connorwhite-online/pneuma/firmware/session/src/state.rs

//! The interaction state machine: Sleep → Connect → Capture → Converse → Forget.
//! Provider- and hardware-agnostic — it drives `dyn Provider` over `dyn` HAL
//! traits, so the same logic runs on mocks (laptop) or real drivers (device).
//! See docs/ARCHITECTURE.md §2.

use std::error::Error;
use std::path::PathBuf;

use crate::config::DeviceConfig;
use crate::hal::{AudioIn, AudioOut, Camera, Modem, WakeReason};
use crate::memory::Memory;
use crate::provider::{MemoryOp, Provider, SessionEvent, SessionOpts};
use crate::tool::ToolRegistry;

const SYSTEM_PROMPT: &str = "You are Pneuma, a concise, warm voice companion. \
Answer briefly. Use the user's memory for context. Only mention what you see when asked.";

#[derive(Debug, Clone, Copy, PartialEq, Eq)]
pub enum State {
    Sleep,
    Connect,
    Capture,
    Converse,
    Forget,
}

pub struct Pneuma {
    mic: Box<dyn AudioIn>,
    speaker: Box<dyn AudioOut>,
    camera: Box<dyn Camera>,
    modem: Box<dyn Modem>,
    provider: Box<dyn Provider>,
    memory: Memory,
    memory_path: PathBuf,
    config: DeviceConfig,
    tools: ToolRegistry,
}

impl Pneuma {
    #[allow(clippy::too_many_arguments)]
    pub fn new(
        mic: Box<dyn AudioIn>,
        speaker: Box<dyn AudioOut>,
        camera: Box<dyn Camera>,
        modem: Box<dyn Modem>,
        provider: Box<dyn Provider>,
        memory: Memory,
        memory_path: PathBuf,
        config: DeviceConfig,
    ) -> Self {
        Pneuma {
            mic,
            speaker,
            camera,
            modem,
            provider,
            memory,
            memory_path,
            config,
            tools: crate::tool::default_registry(),
        }
    }

    pub fn memory(&self) -> &Memory {
        &self.memory
    }

    /// Run one full interaction, triggered by a wake event from the wake island.
    pub fn run_once(&mut self, wake: WakeReason) -> Result<(), Box<dyn Error>> {
        // CONNECT — bring the cellular link up and open a provider session.
        println!("  [state] {:?}", State::Connect);
        if !self.modem.is_online() {
            self.modem.connect();
        }
        let opts = SessionOpts {
            model: self.config.model.clone(),
            memory_context: self.memory.to_context(),
            system_prompt: SYSTEM_PROMPT.to_string(),
        };
        println!(
            "  [provider:{}] starting session (model={}, tier={:?})",
            self.provider.name(),
            opts.model,
            self.provider.tier()
        );
        let (mut session, events) = self.provider.start_session(opts)?;

        // CAPTURE — on demand only; camera is otherwise powered off.
        if wake.wants_vision() {
            println!("  [state] {:?}", State::Capture);
            if let Some(frame) = self.camera.capture() {
                session.push_image(frame)?;
            }
        }

        // CONVERSE — one or more turns within the open session. Each turn streams
        // the user's speech up, then drains the model's reply; the conversation
        // continues while the mic reports a follow-up (VAD) and ends otherwise.
        println!("  [state] {:?}", State::Converse);
        let mut pending: Vec<MemoryOp> = Vec::new();
        let mut turn = 1usize;
        loop {
            if turn > 1 {
                println!("  [state] Converse (follow-up turn {turn})");
            }
            while let Some(chunk) = self.mic.next_chunk() {
                session.push_audio(chunk)?;
            }
            session.end_turn()?;

            for ev in events.iter() {
                match ev {
                    SessionEvent::AudioReply(audio) => self.speaker.play(&audio),
                    SessionEvent::Transcript(t) => println!("  [transcript] {t}"),
                    SessionEvent::MemoryUpdate(op) => {
                        println!("  [memory] proposed: {op:?}");
                        pending.push(op);
                    }
                    SessionEvent::ToolCall { name, args } => {
                        println!("  [tool] {name}({args})");
                        let result = self.tools.run(&name, &args);
                        println!("  [tool] → {result}");
                        session.push_tool_result(&name, result)?;
                    }
                    SessionEvent::TurnComplete => break,
                    SessionEvent::Error(e) => {
                        eprintln!("  [error] {e}");
                        break;
                    }
                }
            }

            if !self.mic.awaiting_followup() {
                break;
            }
            turn += 1;
        }
        session.close();

        // FORGET & SLEEP — apply memory updates, then keep ONLY the memory file.
        println!("  [state] {:?}", State::Forget);
        for op in pending {
            self.memory.apply(op);
        }
        self.memory.compact();
        self.memory.save(&self.memory_path)?;
        println!(
            "  [memory] saved ({} bytes); audio/frames/context discarded",
            self.memory.serialize().len()
        );
        Ok(())
    }
}

#[cfg(test)]
mod tests {
    use super::*;
    use crate::hal::mock::{MockCamera, MockMic, MockModem, MockSpeaker};
    use crate::memory::{Memory, DEFAULT_CAP_BYTES};
    use crate::provider::mock::MockProvider;

    fn device(mic: MockMic, mem: Memory, file: &str) -> Pneuma {
        Pneuma::new(
            Box::new(mic),
            Box::new(MockSpeaker),
            Box::new(MockCamera),
            Box::new(MockModem::offline()),
            Box::new(MockProvider),
            mem,
            std::env::temp_dir().join(file),
            DeviceConfig::default(),
        )
    }

    #[test]
    fn visual_query_updates_memory() {
        let mut d = device(
            MockMic::with_seconds(1),
            Memory::new(DEFAULT_CAP_BYTES),
            "pneuma_test_visual.toml",
        );
        d.run_once(WakeReason::Visual).unwrap();
        assert!(d.memory().facts().iter().any(|f| f.contains("coffee")));
    }

    #[test]
    fn multi_turn_conversation_completes() {
        // A two-turn conversation must drain both turns and return (not hang).
        let mut d = device(
            MockMic::conversation(1, 1),
            Memory::new(DEFAULT_CAP_BYTES),
            "pneuma_test_multiturn.toml",
        );
        d.run_once(WakeReason::WakeWord).unwrap();
    }
}
